adwuard/TrackerKB/hardware/Tracker-Keyboard-PCB/制版说明-PCB-FAB-Note.jpg

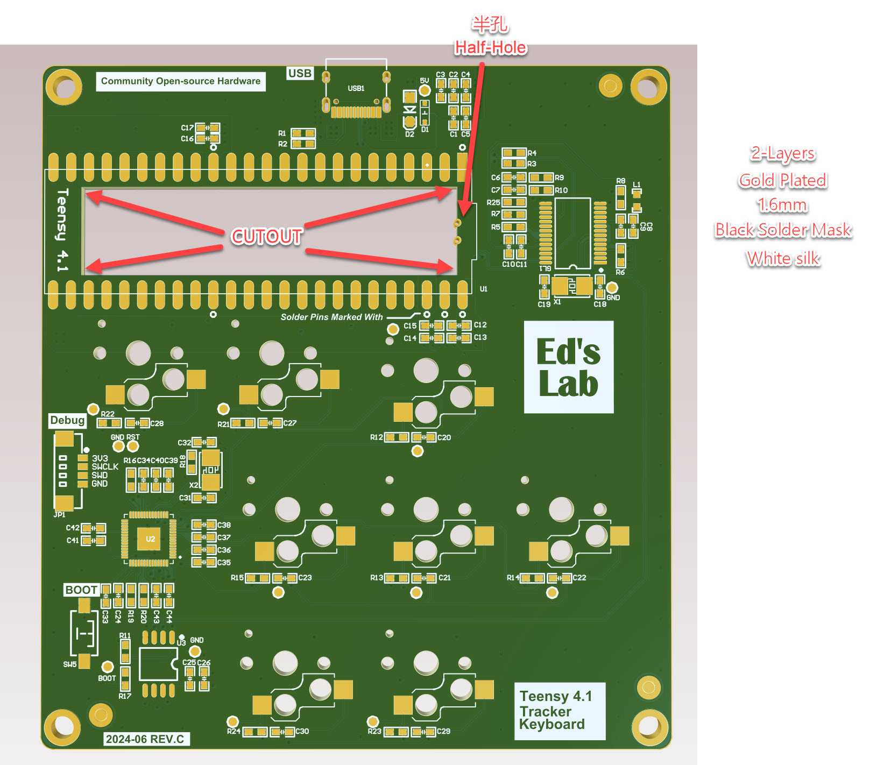
hardware/Tracker-Keyboard-PCB/制版说明-PCB-FAB-Note.jpg
