adwuard/TrackerKB/hardware/Tracker-Keyboard-PCB/钢网说明-Stencil-Note.jpg

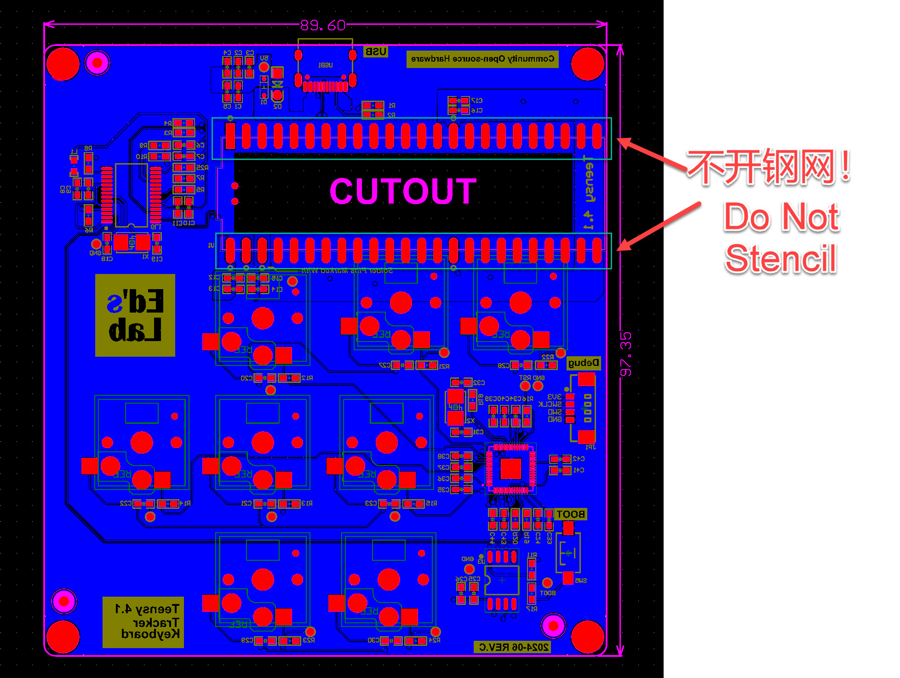
hardware/Tracker-Keyboard-PCB/钢网说明-Stencil-Note.jpg
