adwuard/TrackerKB/image/render/2024-06-14_0-11-16.png

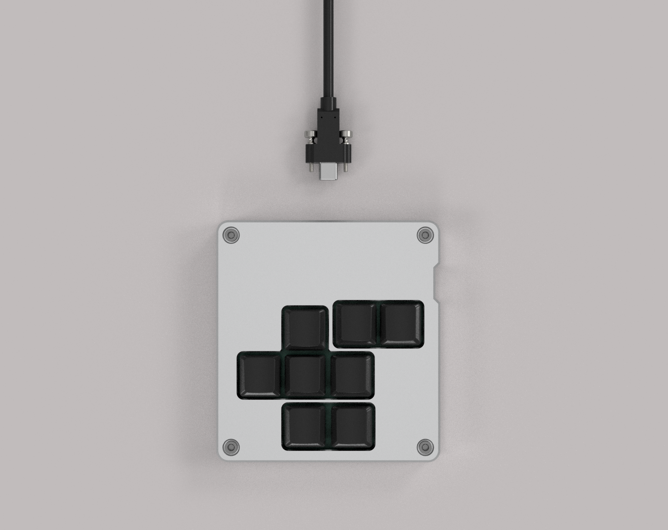
image/render/2024-06-14_0-11-16.png
