adwuard/TrackerKB/image/render/2024-06-14_0-15-20.png

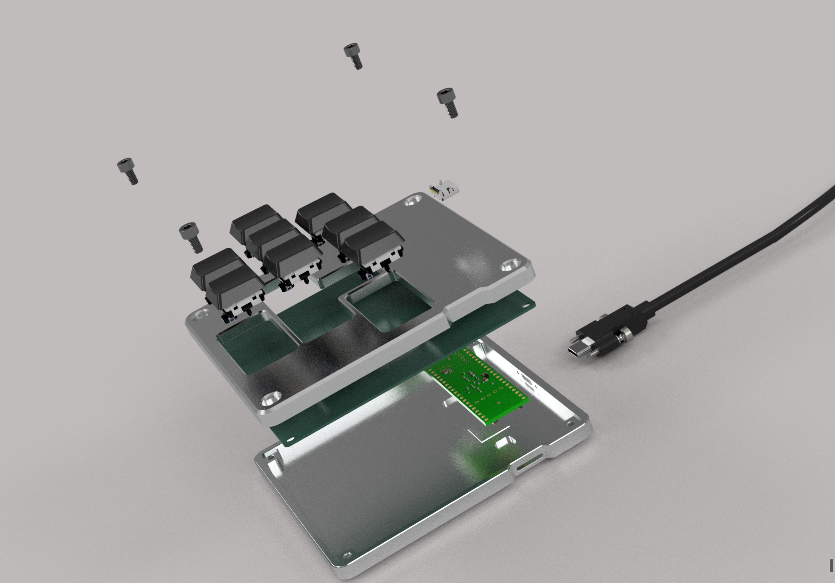
image/render/2024-06-14_0-15-20.png
