adwuard/TrackerKB/image/render/2024-06-14_0-17-35.png

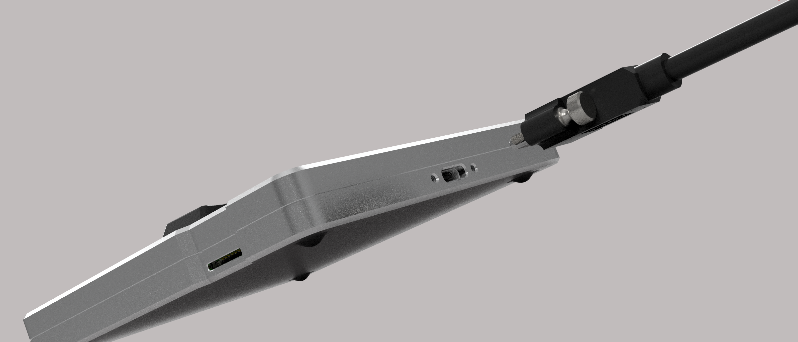
image/render/2024-06-14_0-17-35.png
