adwuard/TrackerKB/image/render/cnc-demo.png

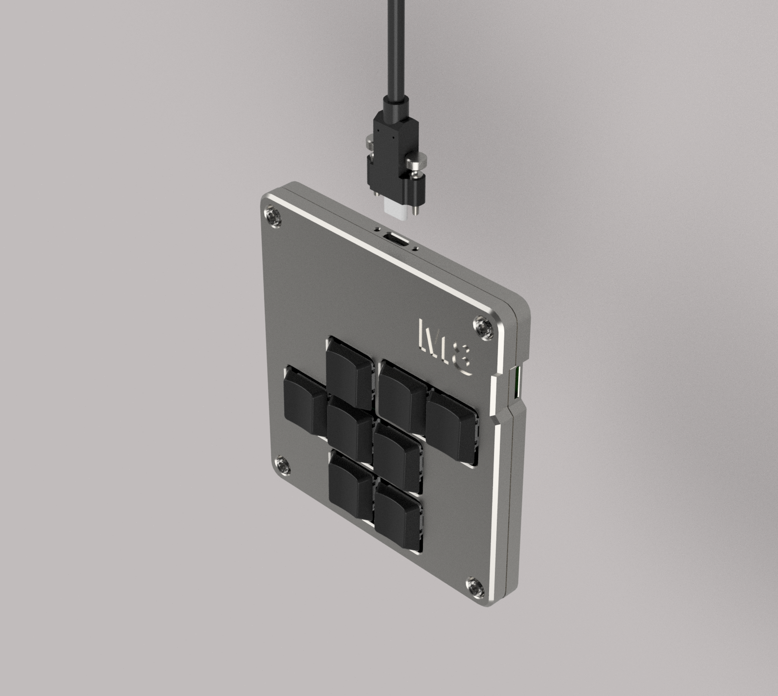
image/render/cnc-demo.png
